OpenNanogrid/ON-socket/cad/renders/ON_Display_C44_2016-Jul-12_01-01-30AM-000_RIGHT.png

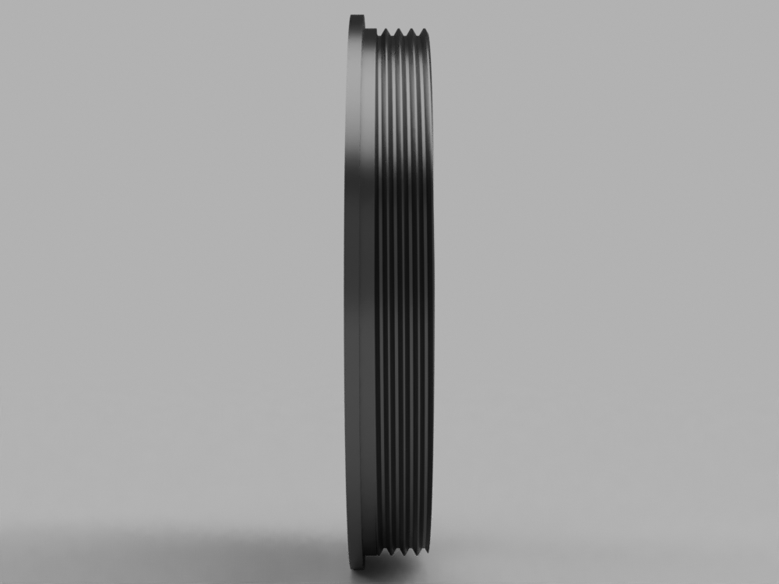
cad/renders/ON_Display_C44_2016-Jul-12_01-01-30AM-000_RIGHT.png
