OpenNanogrid/ON-socket/cad/renders/Wall Socket v4 explode raytraced.png

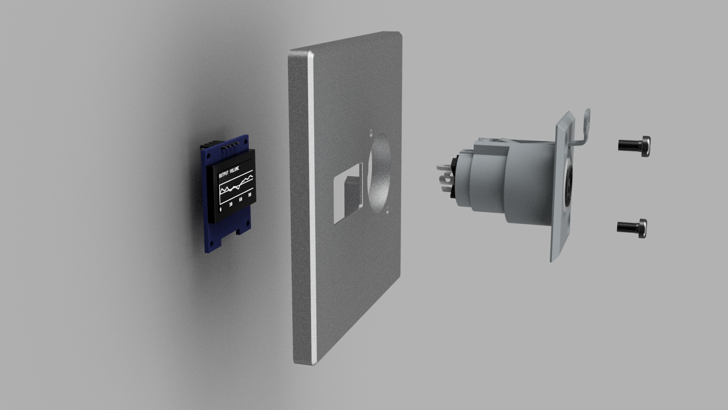
cad/renders/Wall Socket v4 explode raytraced.png
