OpenNanogrid/ON-socket/cad/renders/Wall Socket v4 Front.png

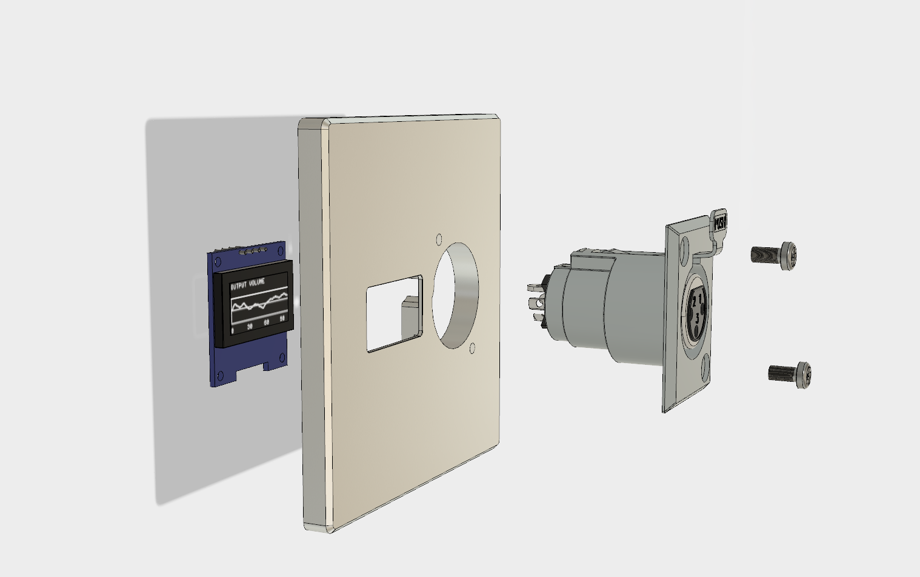
cad/renders/Wall Socket v4 Front.png
