OpenNanogrid/ON-socket/cad/renders/Wall Socket v4 Wireframe.png

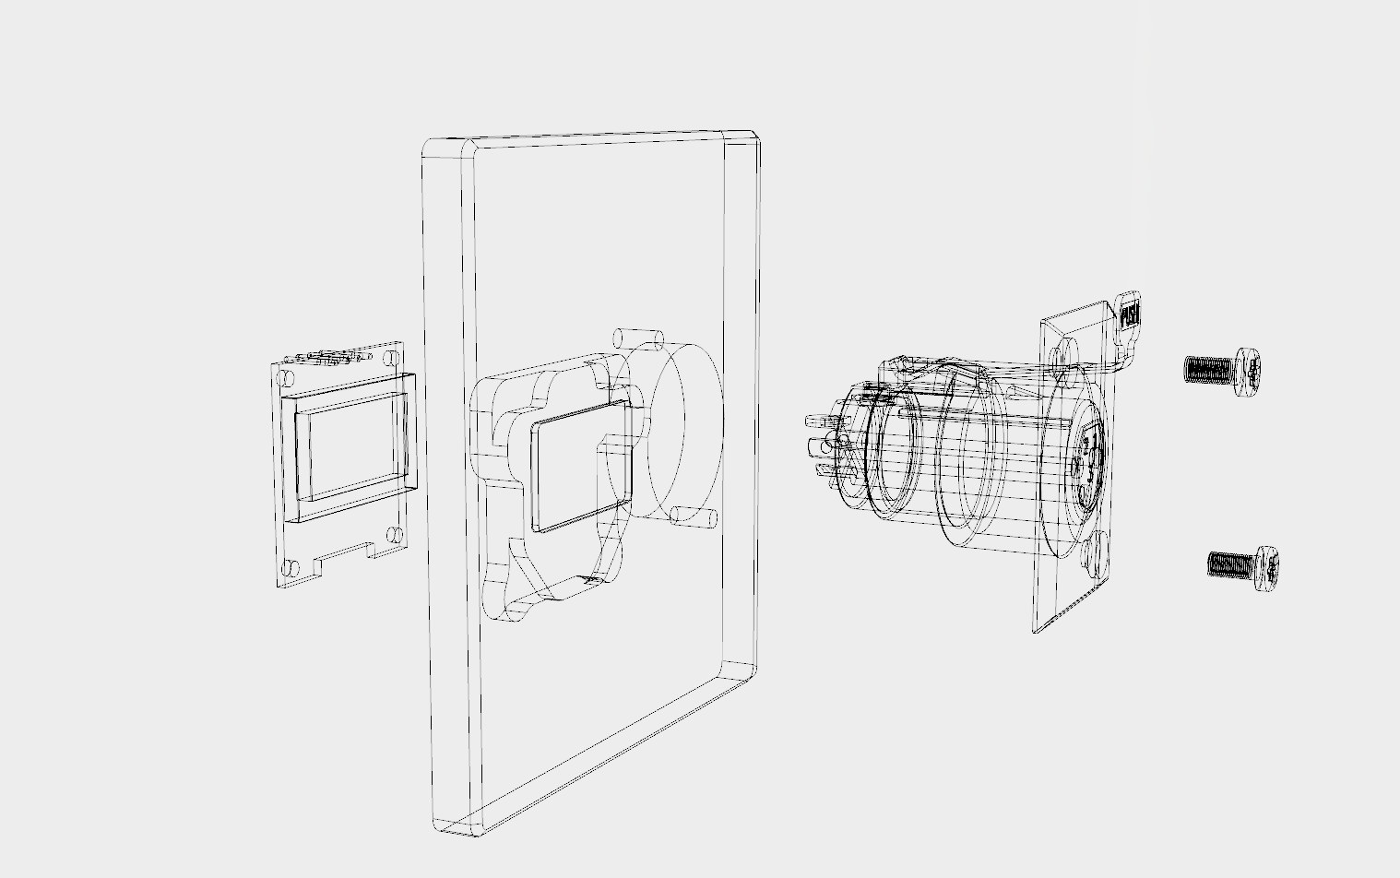
cad/renders/Wall Socket v4 Wireframe.png
