OpenNanogrid/ON-socket/cad/renders/Wall_Socket_Round_Passive_2_x_XLR_+_1_x_USB_2016-Jun-28_02-24-30AM-000_CustomizedView6874958758.png

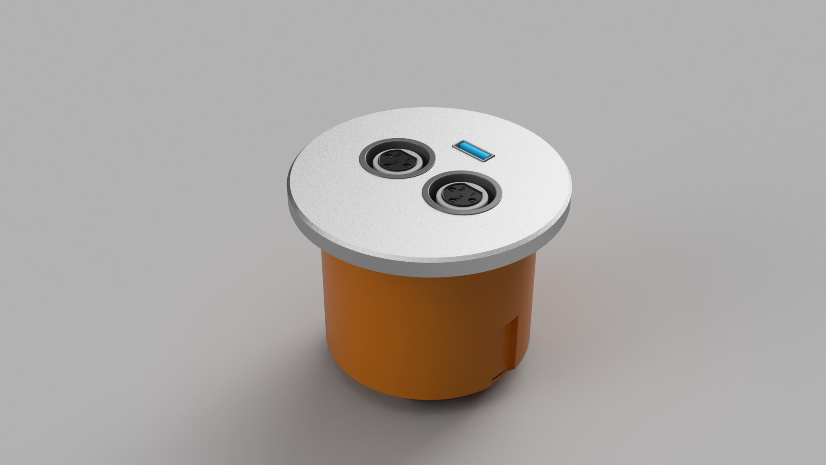
cad/renders/Wall_Socket_Round_Passive_2_x_XLR_+_1_x_USB_2016-Jun-28_02-24-30AM-000_CustomizedView6874958758.png
